Kufferath/-low-cost-particle-counter-based-on-SDS011/Arduino_Code/sds011_screen.jpg

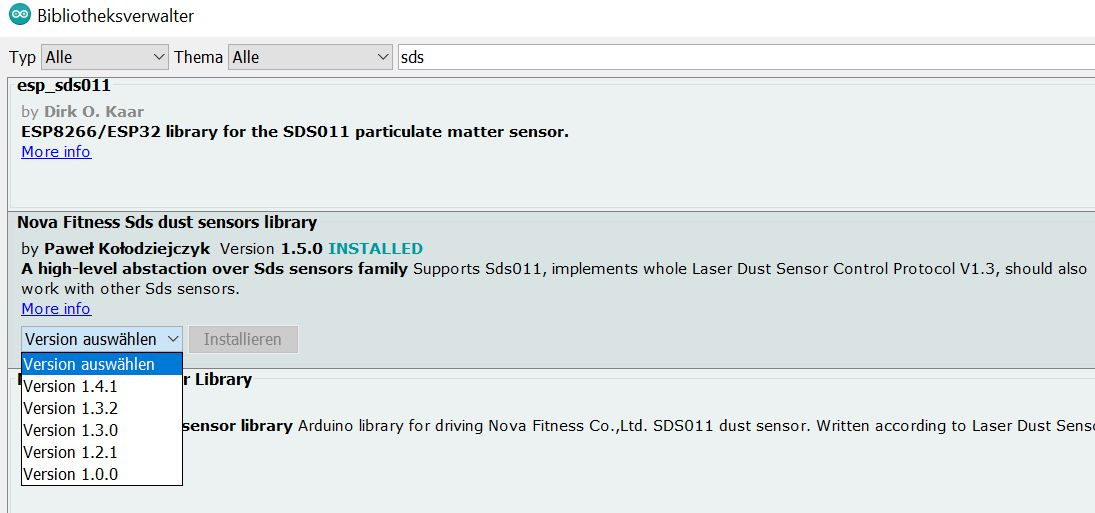
Arduino_Code/sds011_screen.jpg
