Kufferath/-low-cost-particle-counter-based-on-SDS011/Handheld_complet_900.jpg

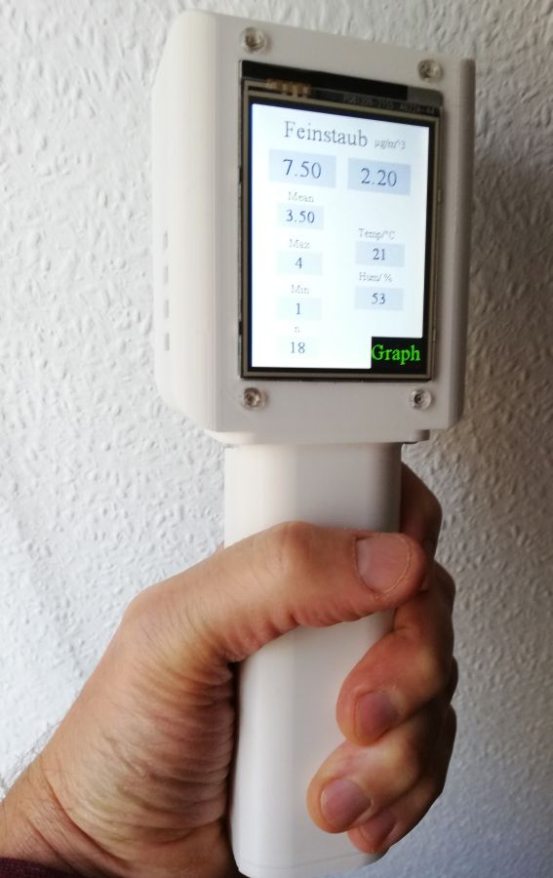
Handheld_complet_900.jpg
