Kufferath/-low-cost-particle-counter-based-on-SDS011/pictures/Arduino_Einbau.jpg

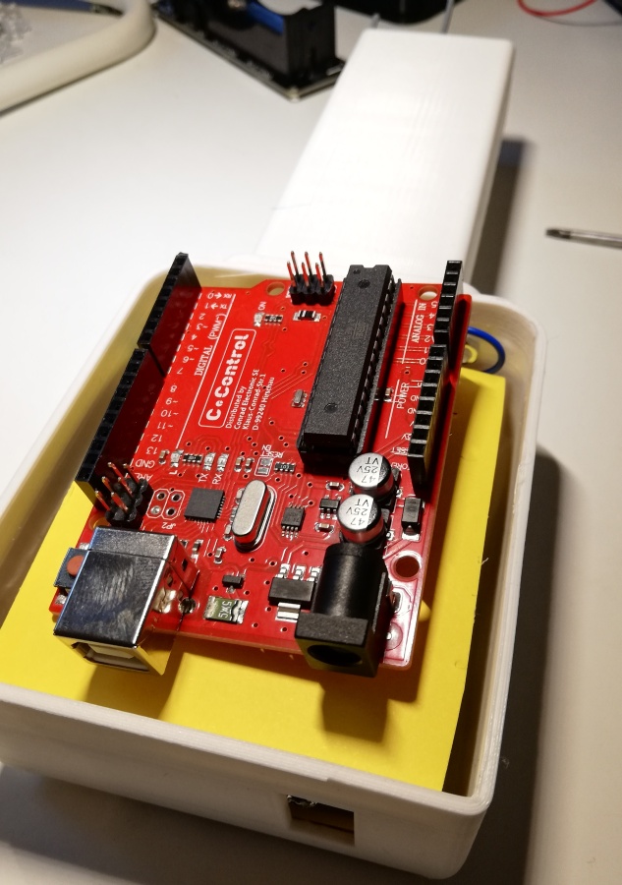
pictures/Arduino_Einbau.jpg
