Kufferath/-low-cost-particle-counter-based-on-SDS011/pictures/Display_Einbau_2.jpg

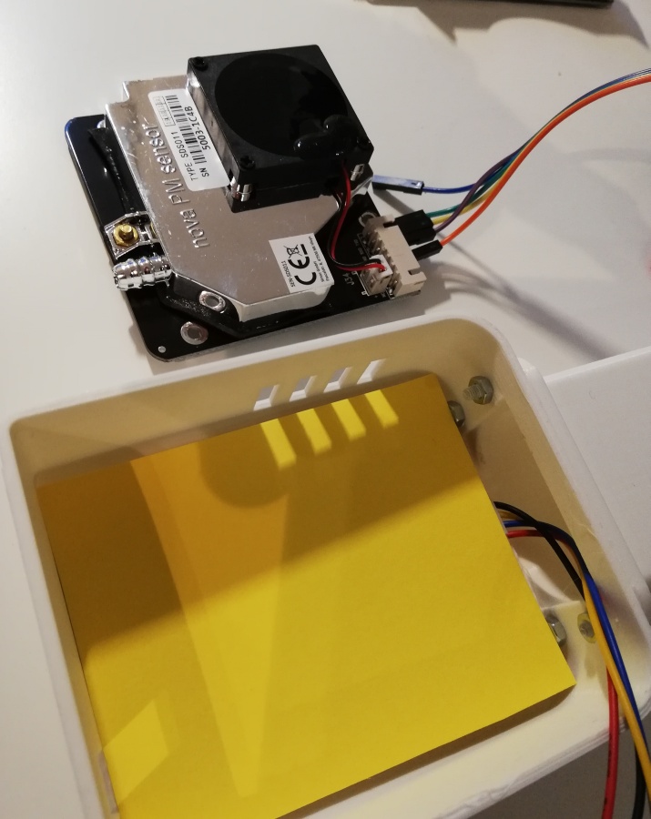
pictures/Display_Einbau_2.jpg
