Kufferath/-low-cost-particle-counter-based-on-SDS011/pictures/Display_Graf.jpg

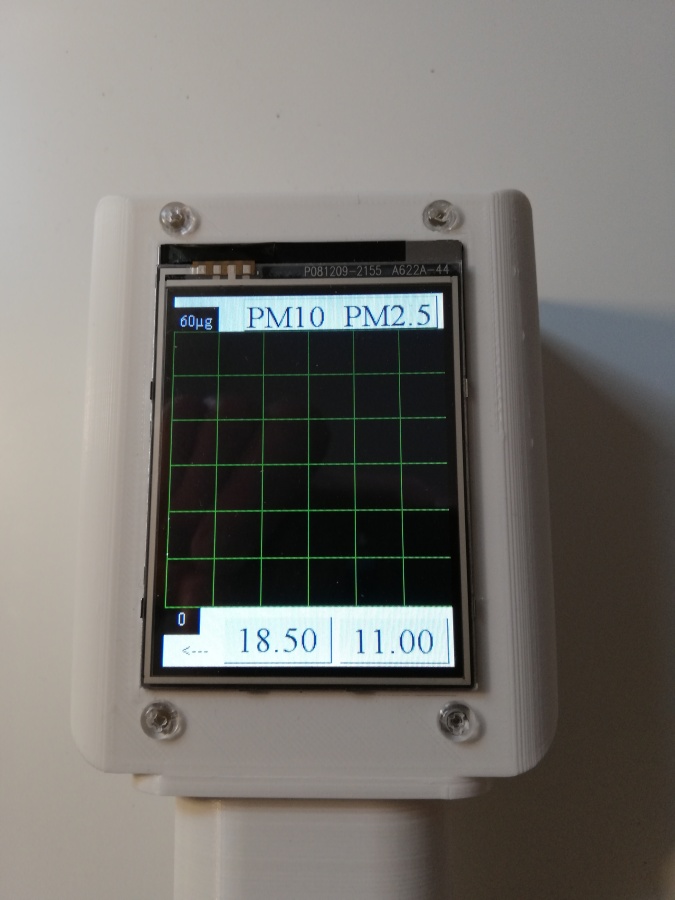
pictures/Display_Graf.jpg
