Kufferath/-low-cost-particle-counter-based-on-SDS011/pictures/Gerät_kompl_1.jpg

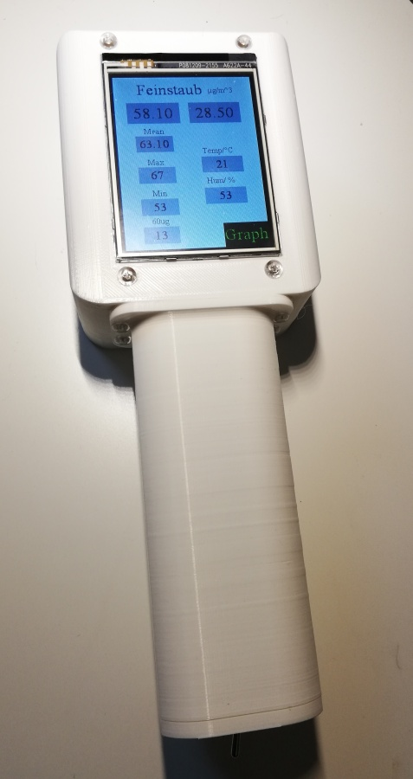
pictures/Gerät_kompl_1.jpg
