Kufferath/-low-cost-particle-counter-based-on-SDS011/pictures/Gerät_komplett_2b.jpg

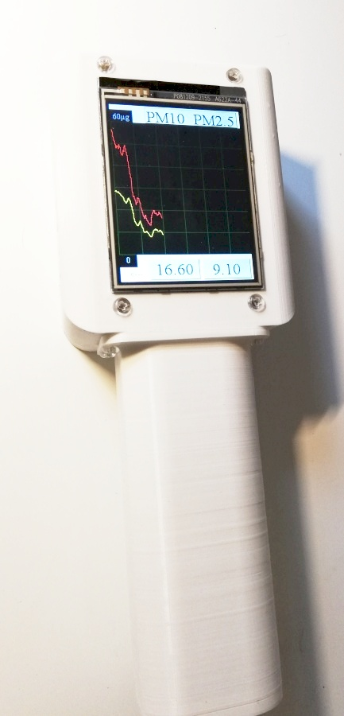
pictures/Gerät_komplett_2b.jpg
