Kufferath/-low-cost-particle-counter-based-on-SDS011/pictures/Schaltplan_Fritzing.JPG

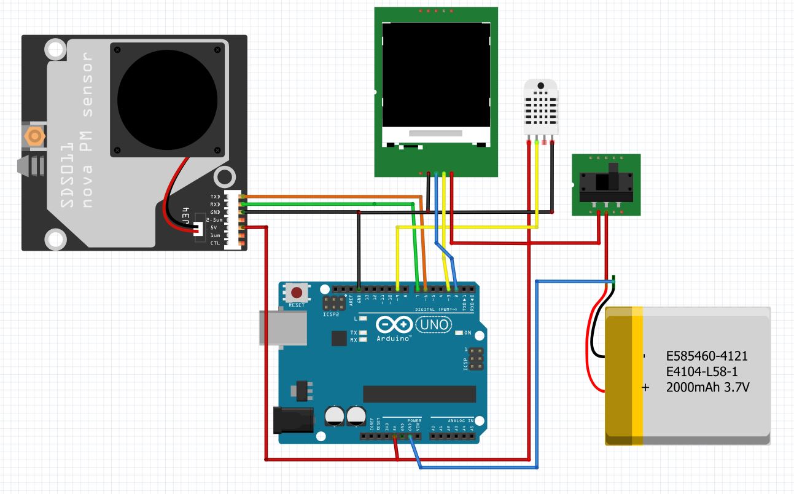
pictures/Schaltplan_Fritzing.JPG
