Kufferath/-low-cost-particle-counter-based-on-SDS011/pictures/SDS011_Einbau_A.jpg

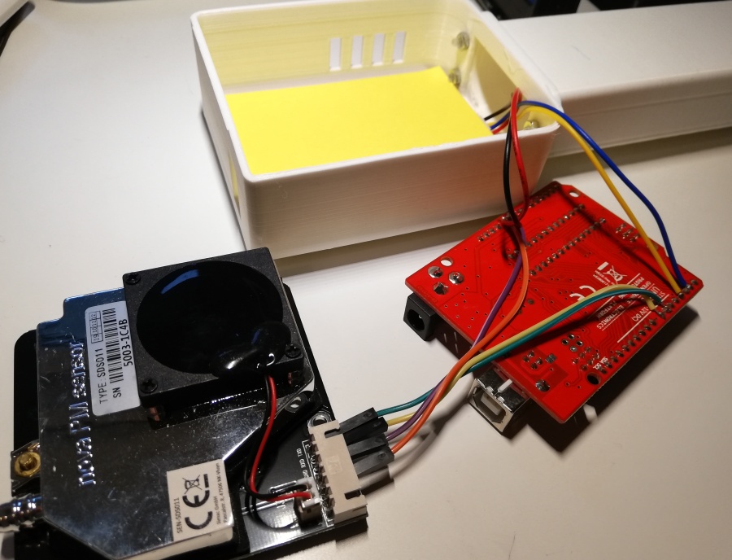
pictures/SDS011_Einbau_A.jpg
